OlegDemk/stm32F401CCU_NTF24L01_RX_TX_Sleep/1. TX/Core/Inc/DS3231/main_ds3231.h

/*
 * main_ds3231.h
 *
 *  Created on: Jun 26, 2024
 *      Author: odemki
 */

#ifndef INC_DS3231_MAIN_DS3231_H_
#define INC_DS3231_MAIN_DS3231_H_

void read_time(char * buff);

#endif /* INC_DS3231_MAIN_DS3231_H_ */
